nurikabe-uec/cad/motor_joint_150slit.stl

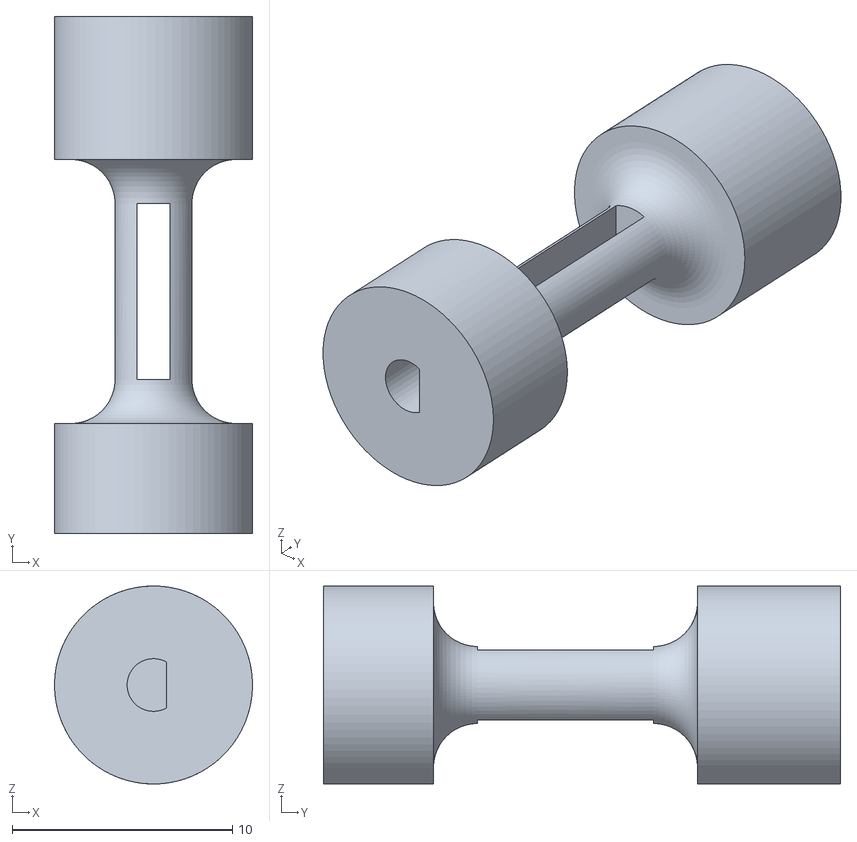
[picture p6: CAD file, 2019-12-10]
motor_joint_150slit.stl
9.00 x 23.5 x 9.00
