nurikabe-uec/cad/motor_joint_for_photon_insertnut.stl

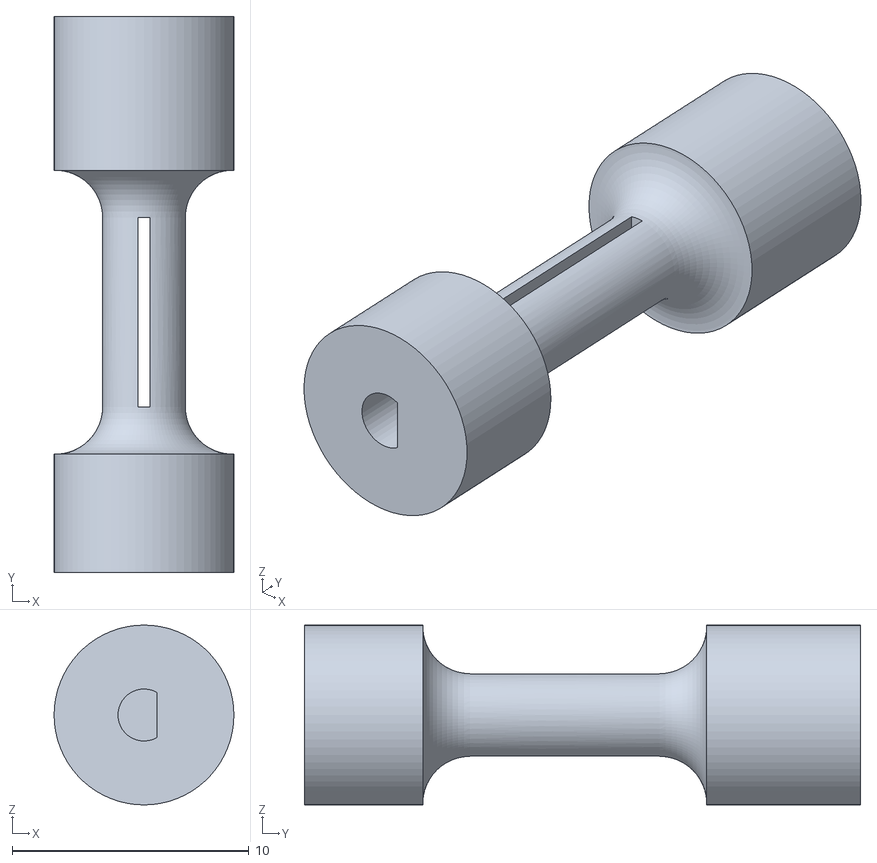
[picture p7: CAD file, 2019-12-02]
motor_joint_for_photon_insertnut.stl
7.60 x 23.5 x 7.60
