nurikabe-uec/cad/jikuuke_ver2_7_7mm.stl

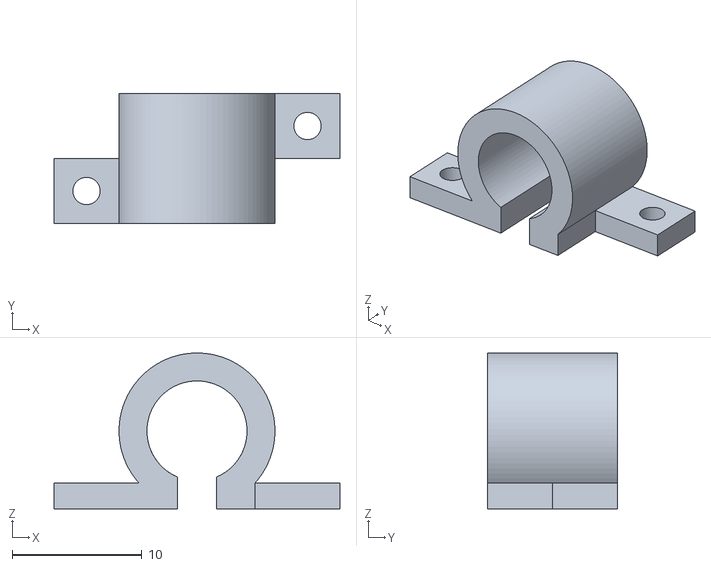
[picture p8: CAD file, 2019-11-25]
jikuuke_ver2_7_7mm.stl
22.0 x 10.0 x 12.0
