nurikabe-uec/cad/motor_joint_for_photon_2_4mm.stl

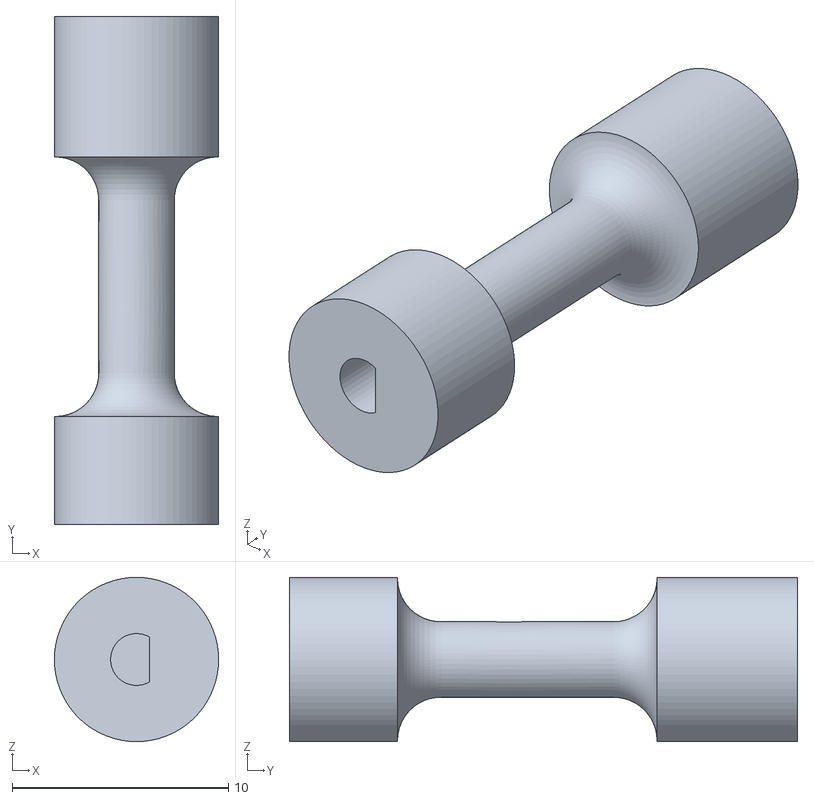
[picture p9: CAD file, 2019-11-25]
motor_joint_for_photon_2_4mm.stl
7.60 x 23.5 x 7.60
