nurikabe-uec/cad/motor_joint_for_photon_insertnut_2_4mm.stl

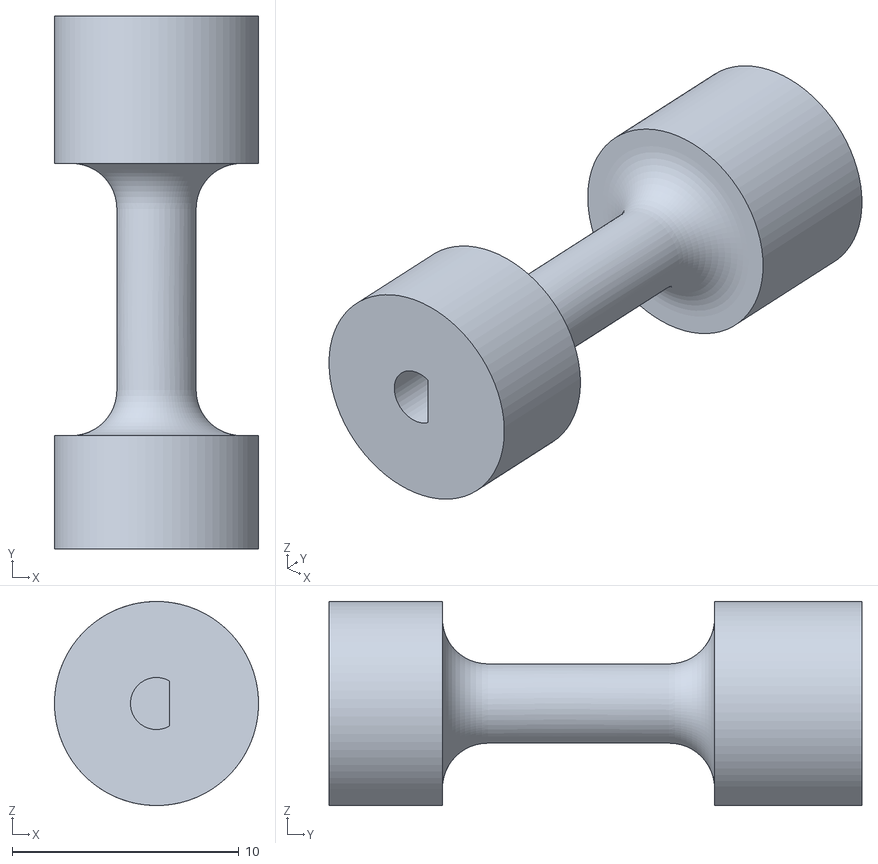
[picture p10: CAD file, 2019-11-25]
motor_joint_for_photon_insertnut_2_4mm.stl
9.00 x 23.5 x 9.00
