nurikabe-uec/cad/pin_joint_plastic_v4.stl

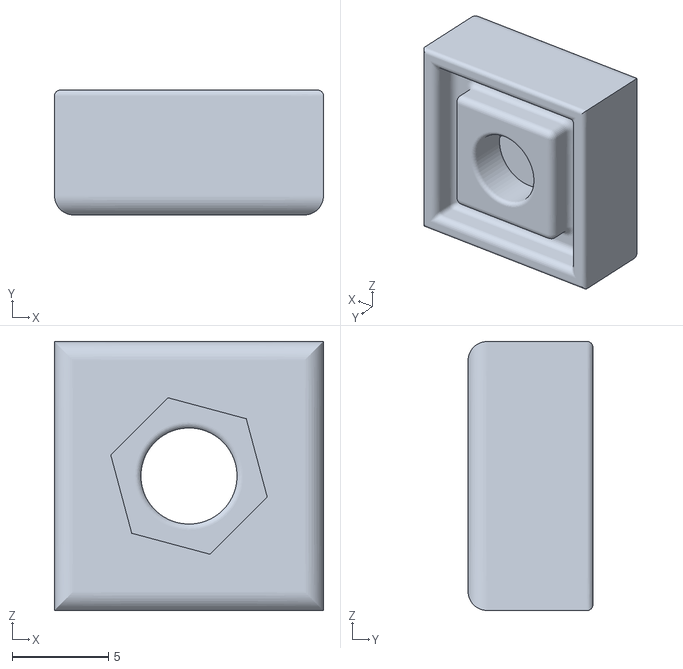
[picture p11: CAD file, 2019-11-25]
pin_joint_plastic_v4.stl
14.0 x 6.50 x 14.0
