nurikabe-uec/cad/photon_sample.stl

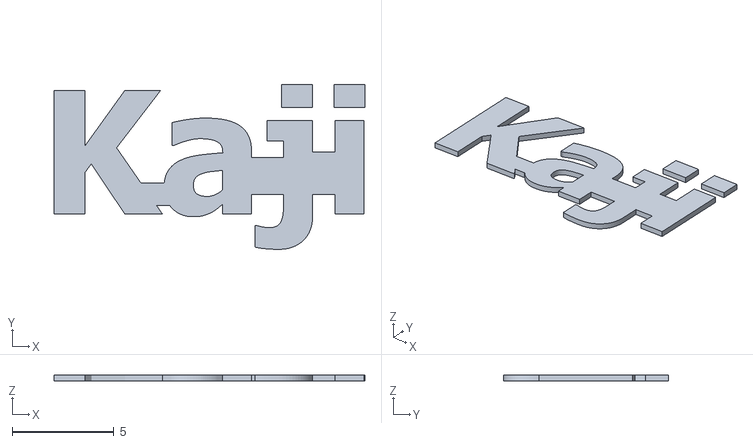
[picture p12: CAD file, 2019-11-01]
photon_sample.stl
15.3 x 8.11 x 0.3
