nurikabe-uec/cad/photon_sample_square.stl

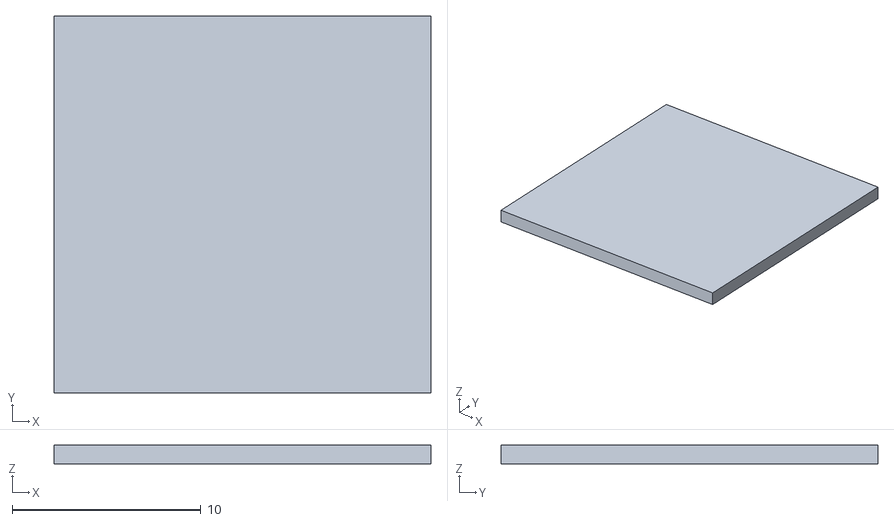
[picture p13: CAD file, 2019-11-01]
photon_sample_square.stl
20.0 x 20.0 x 1.00
