nurikabe-uec/cad/motor_joint_for_photon.stl

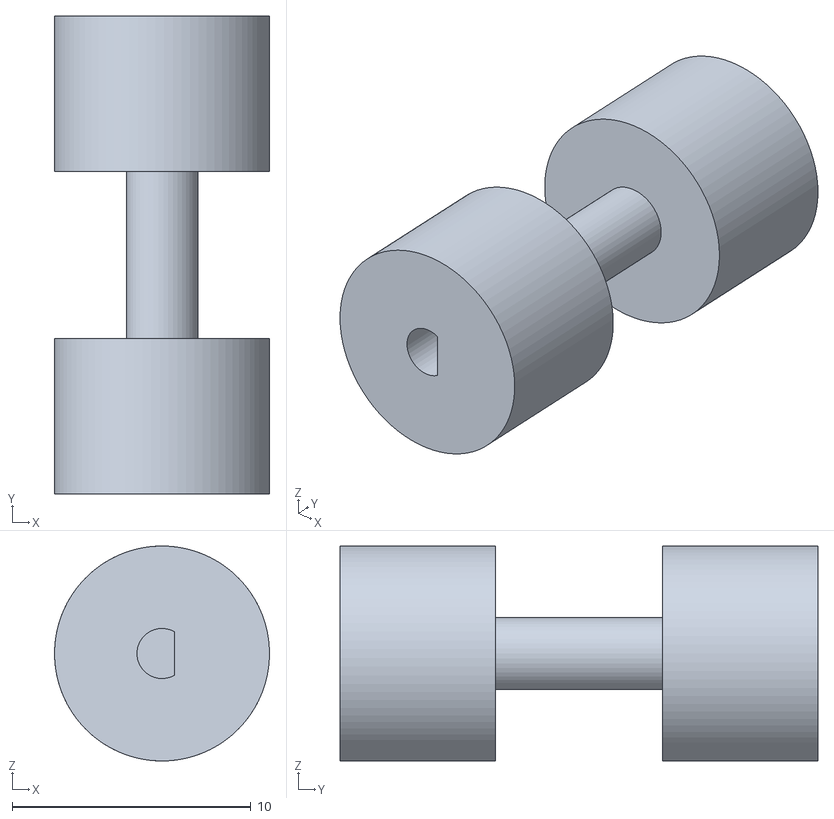
[picture p14: CAD file, 2019-10-25]
motor_joint_for_photon.stl
9.00 x 20.0 x 9.00
