nurikabe-uec/cad/motor_joint.stl

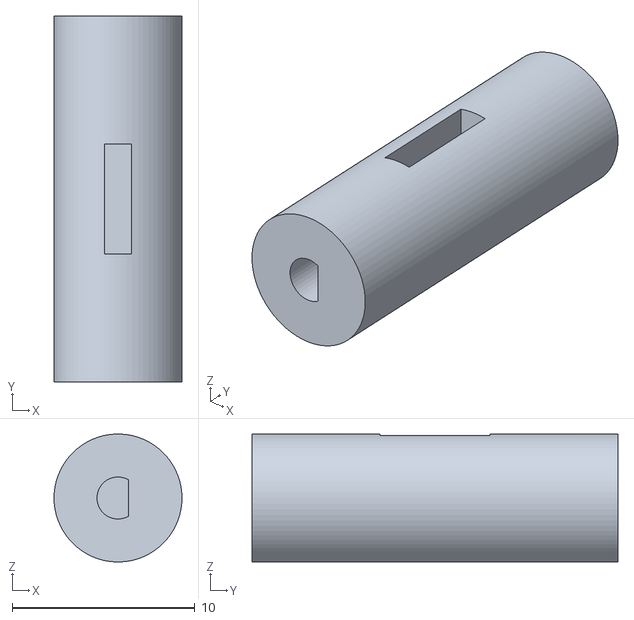
[picture p15: CAD file, 2019-10-25]
motor_joint.stl
7.00 x 20.0 x 6.99
