nurikabe-uec/cad/motor_and_pin_joint_m4.stl

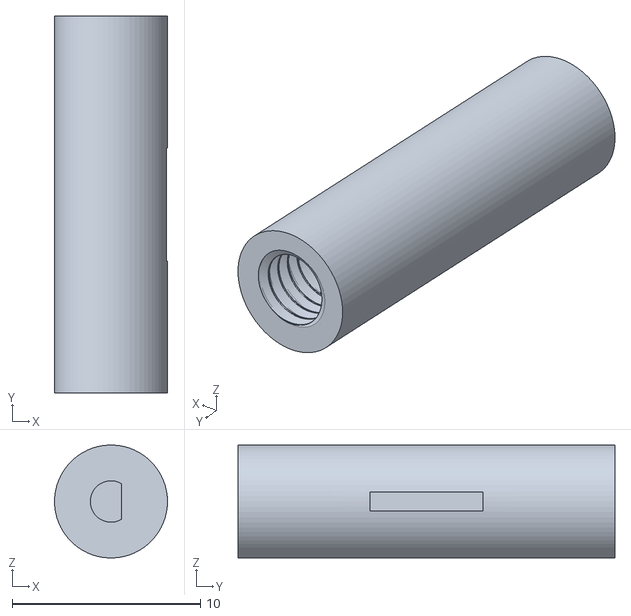
[picture p16: CAD file, 2019-10-14]
motor_and_pin_joint_m4.stl
6.00 x 20.0 x 5.99
