nurikabe-uec/cad/pin_joint_ver5_for_plstc_0940.stl

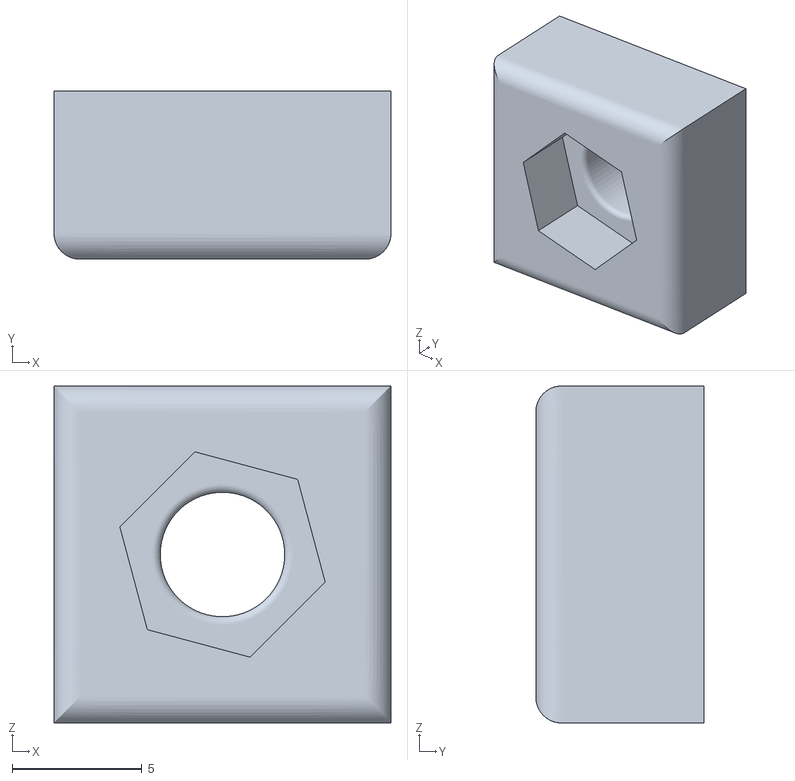
[picture p17: CAD file, 2019-10-14]
pin_joint_ver5_for_plstc_0940.stl
13.0 x 6.50 x 13.0
