nurikabe-uec/cad/pin_joint_ver2_1.stl

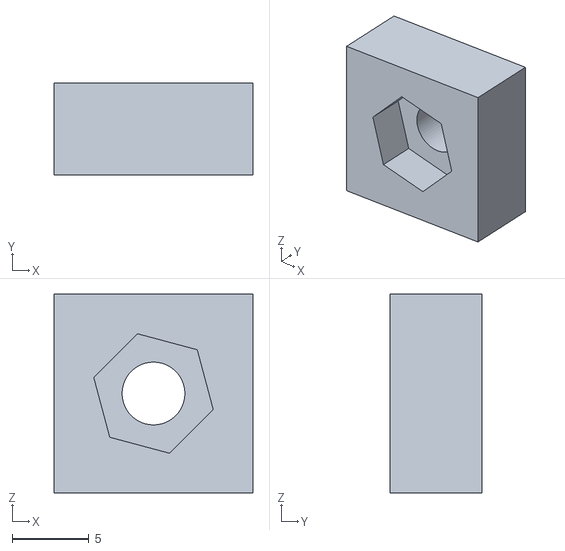
[picture p18: CAD file, 2019-10-04]
pin_joint_ver2_1.stl
13.0 x 6.00 x 13.0
